bkw777/M4ROM/PCB/out/M4ROM_programming_adapter.bottom.jpg

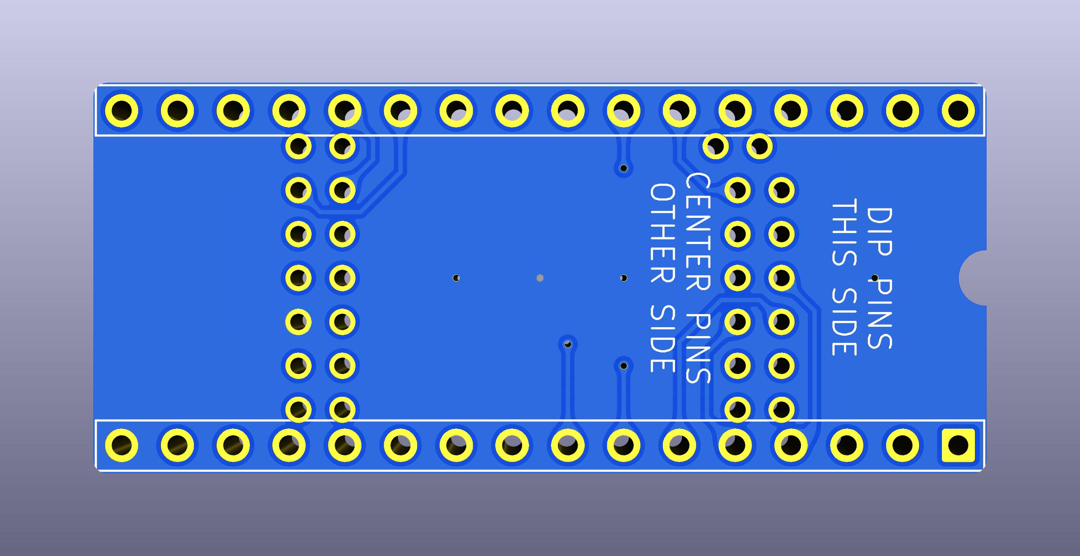
PCB/out/M4ROM_programming_adapter.bottom.jpg
